Escrich/00-Filamentalist_Rewinder_Escrich_modifications-00/20250526 Modified drive roller/Modified drive roller.JPG

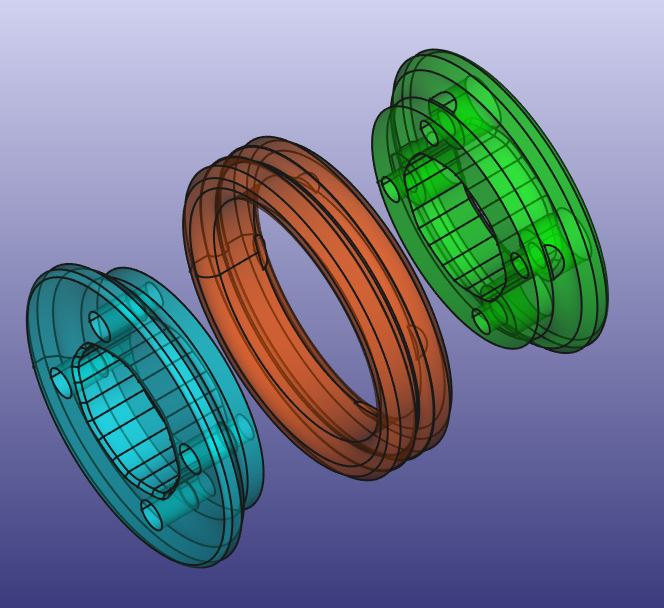
20250526 Modified drive roller/Modified drive roller.JPG
