Escrich/00-Filamentalist_Rewinder_Escrich_modifications-00/20250526 Modified Rim roller/Rim roller with locking screw/20250528 Half Rim roller with square nut and locking screw (01).JPG

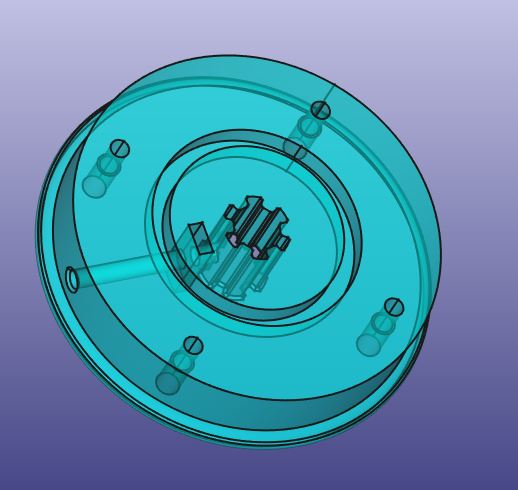
20250526 Modified Rim roller/Rim roller with locking screw/20250528 Half Rim roller with square nut and locking screw (01).JPG
