Escrich/00-Filamentalist_Rewinder_Escrich_modifications-00/20250529 Back roller two units/20250529 Back Rollers two units 688 bearings  (1).JPG

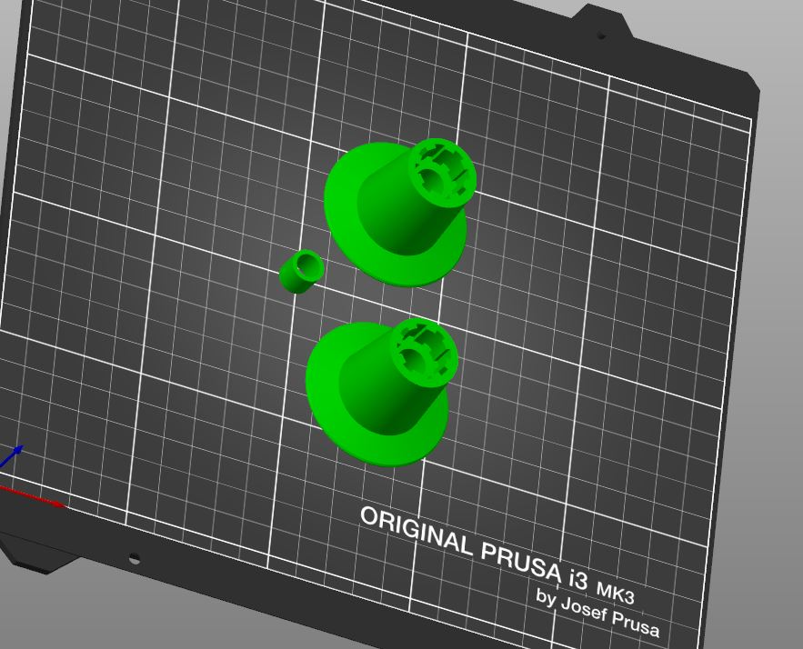
20250529 Back roller two units/20250529 Back Rollers two units 688 bearings (1).JPG
